tltangliang/10inch-player/01.structure/acrylic color 834.png

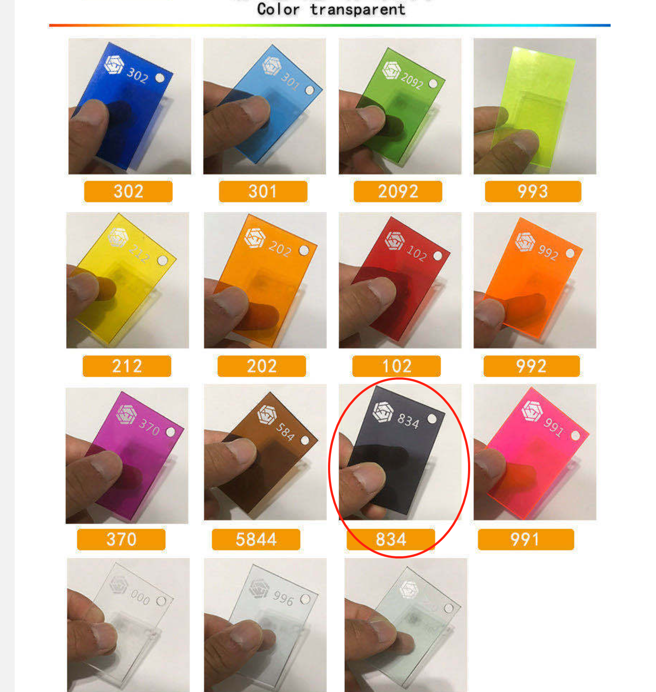
01.structure/acrylic color 834.png
