tltangliang/10inch-player/image/00.jpg

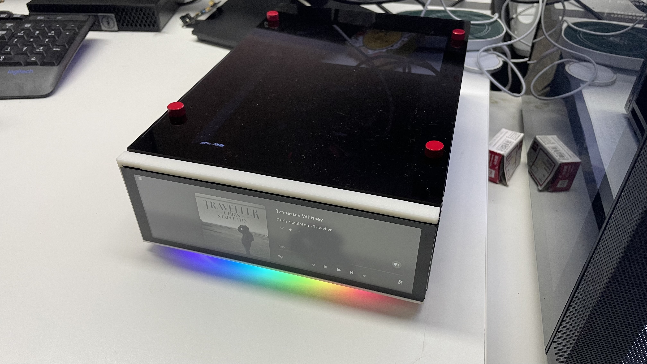
image/00.jpg
