tltangliang/10inch-player/image/04.png

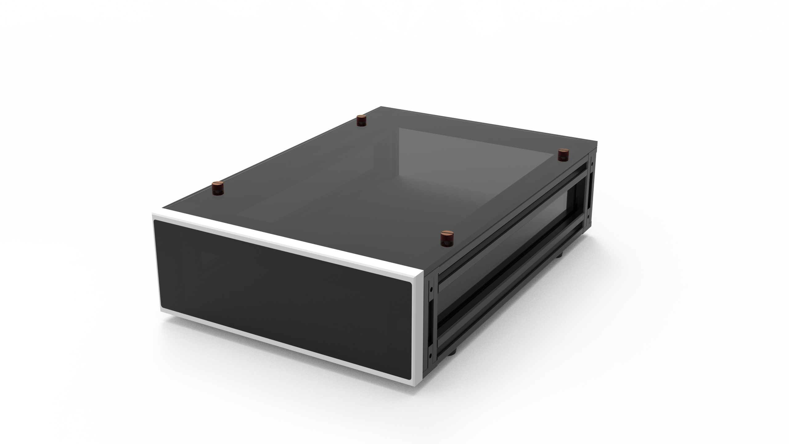
image/04.png
