tltangliang/10inch-player/01.structure/acrylic side.SLDPRT

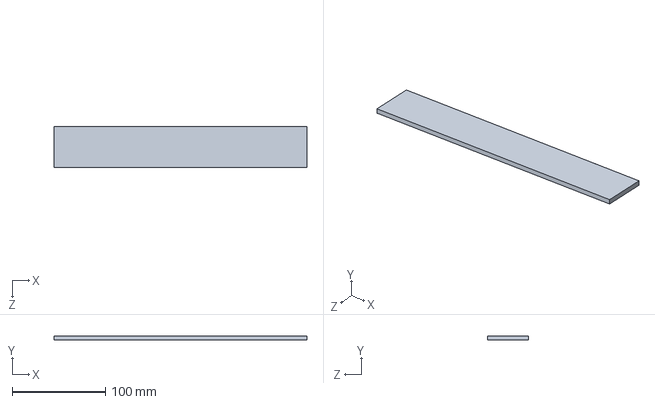
[picture p34: CAD file, 2023-05-24]
01.structure/acrylic side.SLDPRT
272.0 x 4.65 x 44.0 mm
