tltangliang/10inch-player/01.structure/2020 D 260mm.SLDPRT

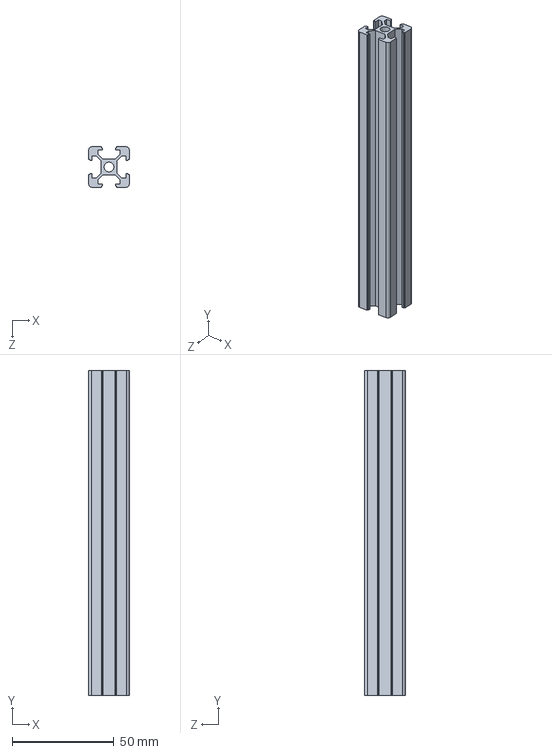
[picture p35: CAD file, 2023-05-24]
01.structure/2020 D 260mm.SLDPRT
20.0 x 160.0 x 20.0 mm
