tltangliang/10inch-player/01.structure/2020 slider nut M4.SLDPRT

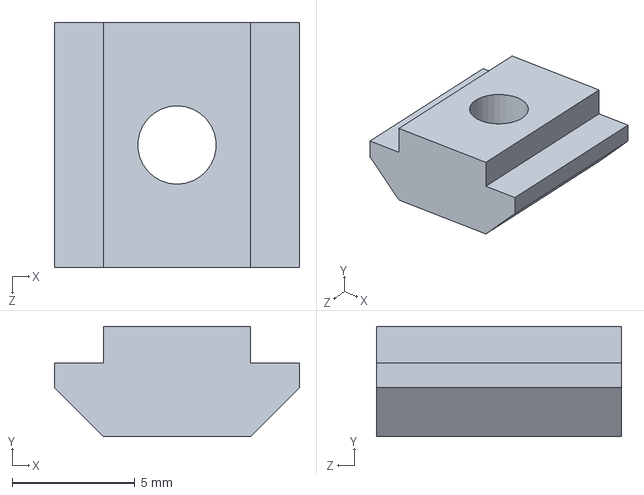
[picture p36: CAD file, 2023-05-24]
01.structure/2020 slider nut M4.SLDPRT
10.0 x 4.50 x 10.0 mm
